8BitMixtape/MutanMonkey_Mixtape3000/graphics/MutanMonkey_2d_render.png

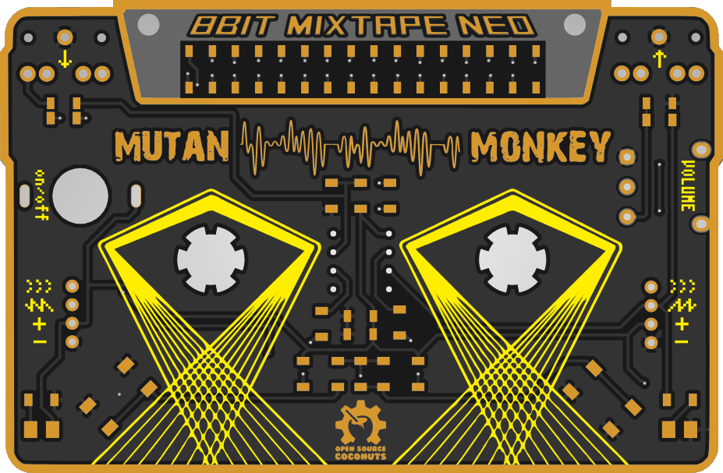
graphics/MutanMonkey_2d_render.png
