8BitMixtape/MutanMonkey_Mixtape3000/graphics/MutanMonkey_2d_render_back.png

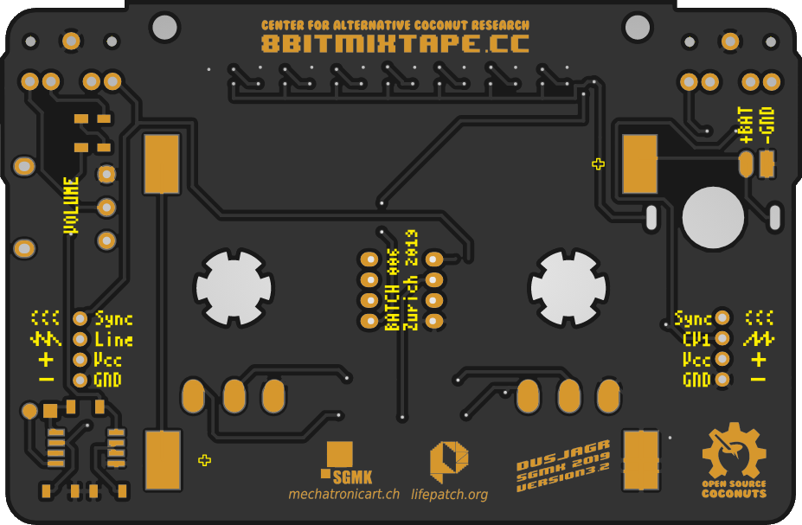
graphics/MutanMonkey_2d_render_back.png
