8BitMixtape/MutanMonkey_Mixtape3000/graphics/MutanMonkey_draft.png

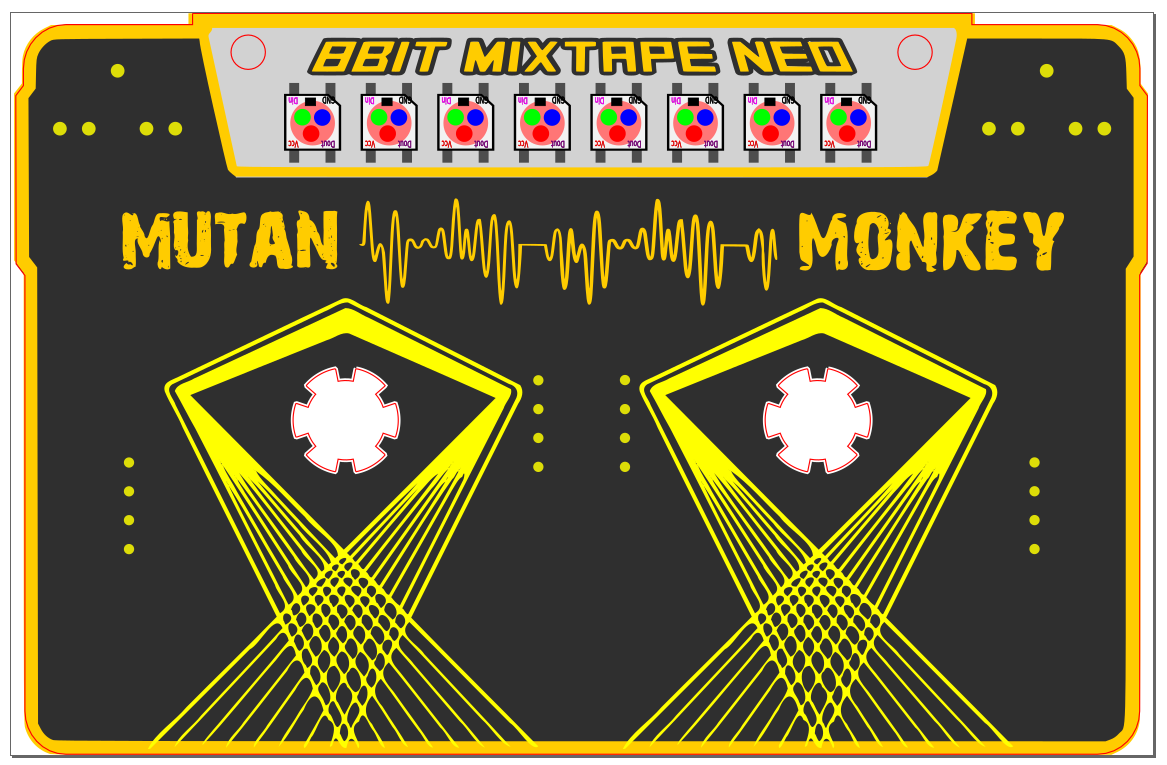
graphics/MutanMonkey_draft.png
