8BitMixtape/MutanMonkey_Mixtape3000/graphics/Plantilla tarjeta trasera 290817.jpg

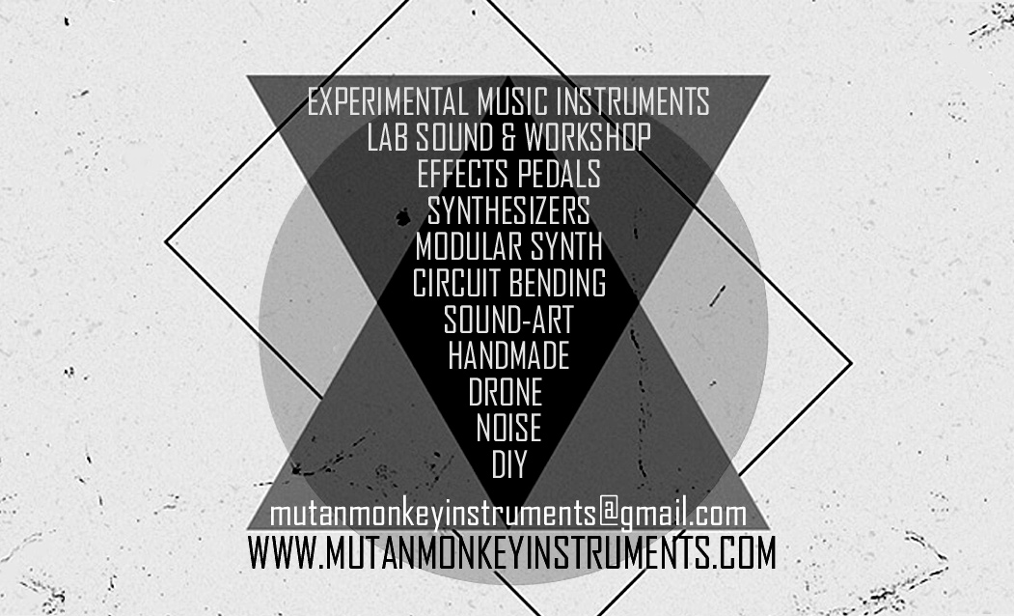
graphics/Plantilla tarjeta trasera 290817.jpg
