8BitMixtape/MutanMonkey_Mixtape3000/graphics/Workshop_flyer.jpg

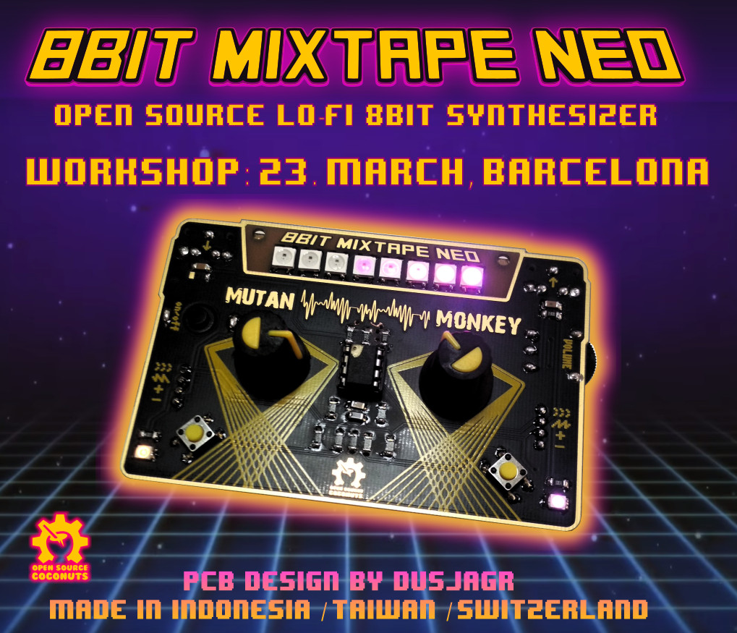
graphics/Workshop_flyer.jpg
