8BitMixtape/MutanMonkey_Mixtape3000/photos/IMG_20190413_114406.jpg

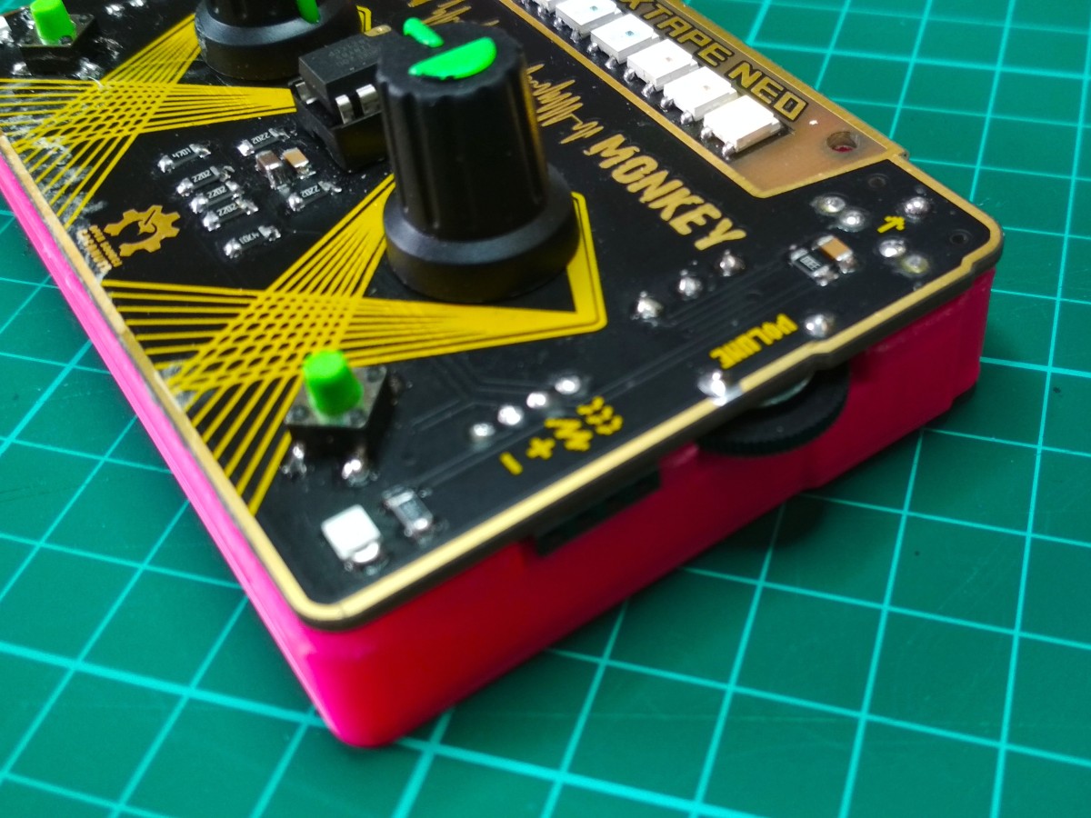
photos/IMG_20190413_114406.jpg
